bitaxeorg/supraHex/3d/TL3340AF160QG.step

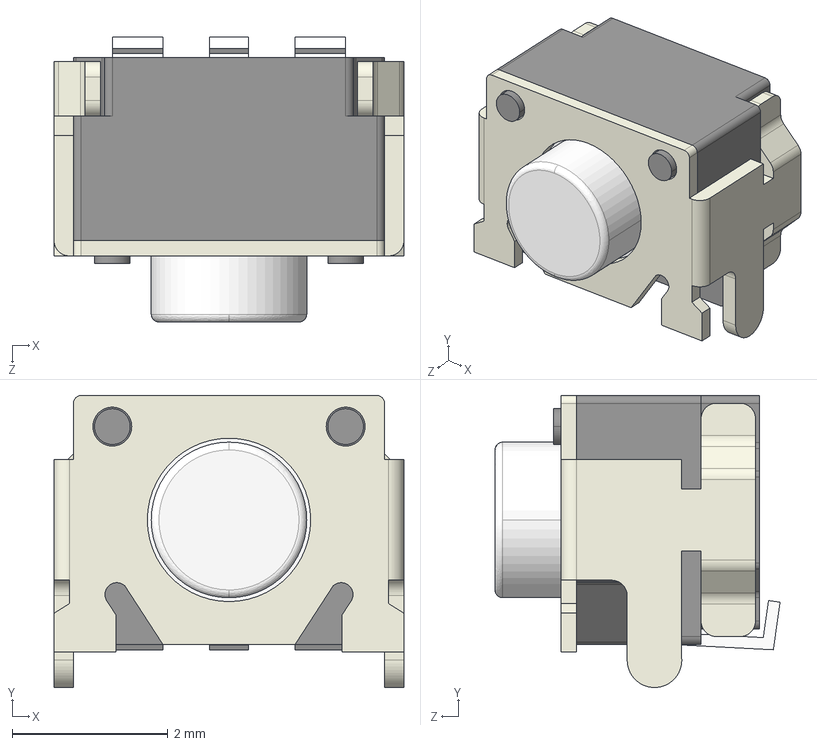
[picture p22: CAD file, 2024-08-30]
3d/TL3340AF160QG.step
4.50 x 3.76 x 3.67 mm
