bitaxeorg/supraHex/3d/heatsink.step

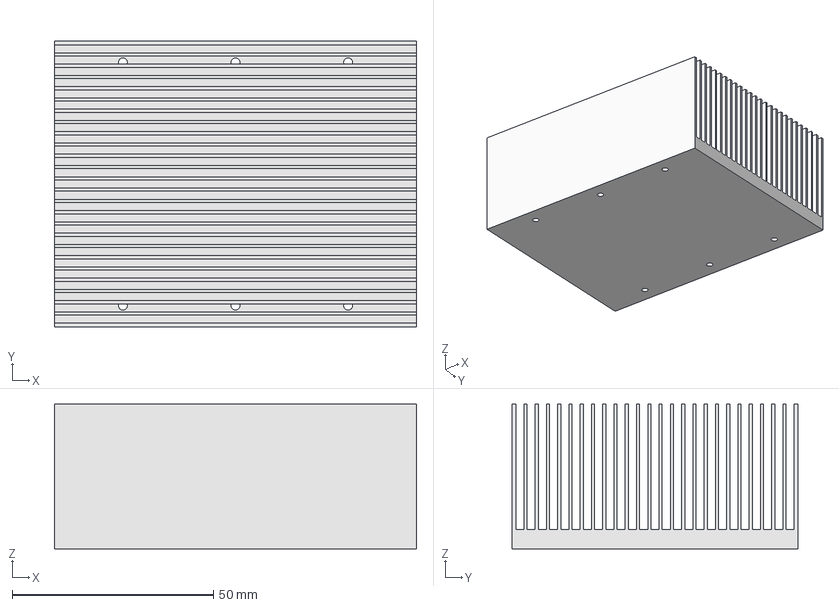
[picture p24: CAD file, 2024-08-30]
3d/heatsink.step
90.0 x 71.0 x 36.0 mm
