bitaxeorg/supraHex/3d/SN74AXC1T45DBVR.STEP

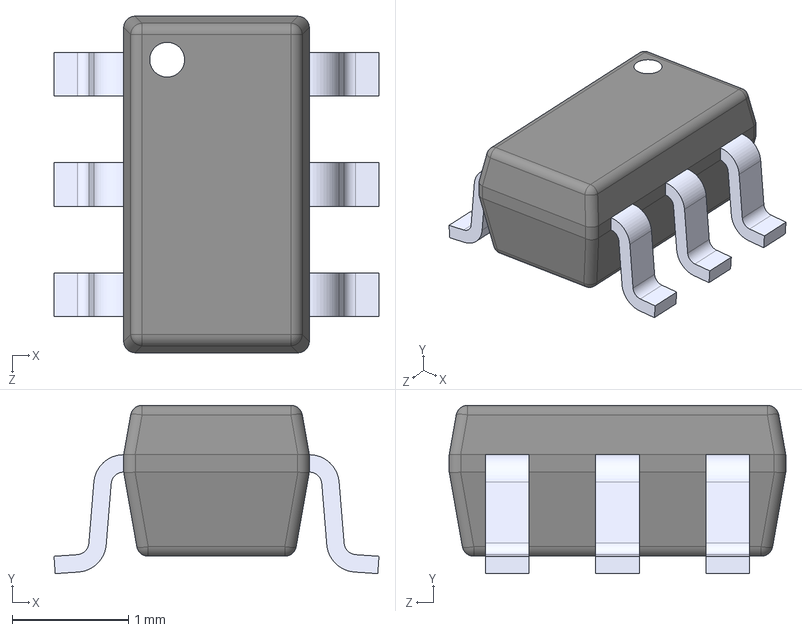
[picture p25: CAD file, 2024-08-30]
3d/SN74AXC1T45DBVR.STEP
2.80 x 1.45 x 2.90 mm
