bitaxeorg/supraHex/3d/RUM0016A.stp

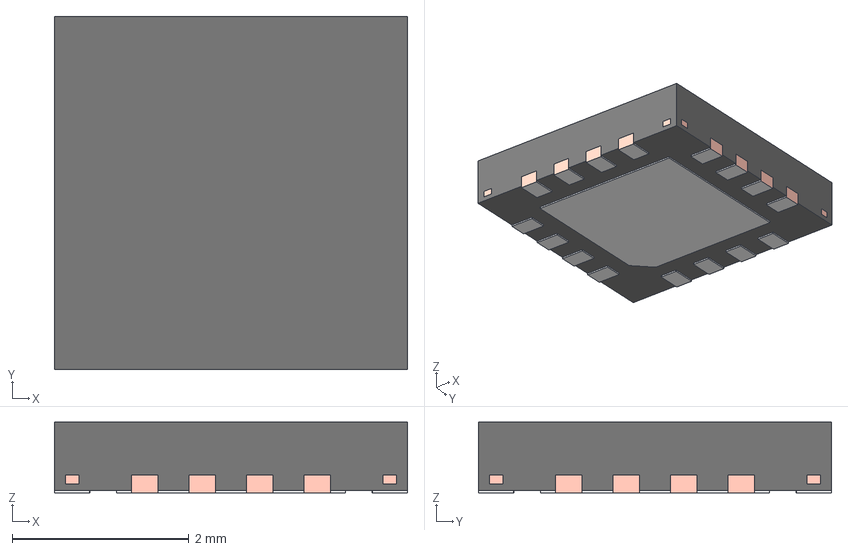
[picture p28: CAD file, 2024-08-30]
3d/RUM0016A.stp
4.00 x 4.00 x 0.8 mm
FRAME
PIN1_AREA
