bitaxeorg/supraHex/3d/bm1366.STP

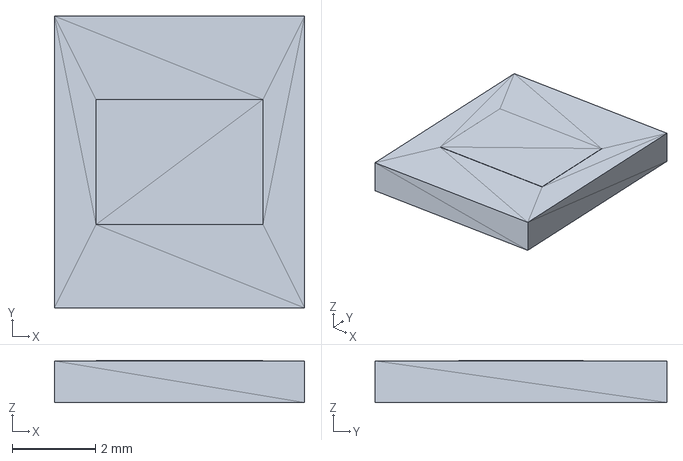
[picture p29: CAD file, 2024-08-30]
3d/bm1366.STP
6.00 x 7.00 x 1.01 mm
