bitaxeorg/supraHex/3d/EVQ-9P701P.stp

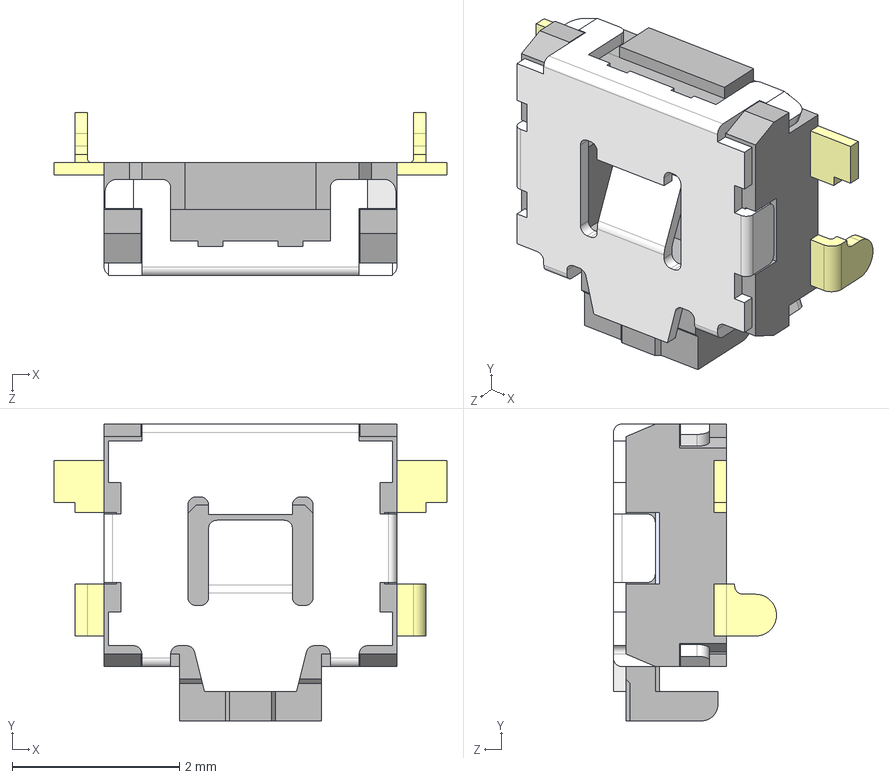
[picture p30: CAD file, 2024-08-30]
3d/EVQ-9P701P.stp
4.70 x 3.55 x 1.95 mm
