bitaxeorg/supraHex/3d/SMV_z90.stp

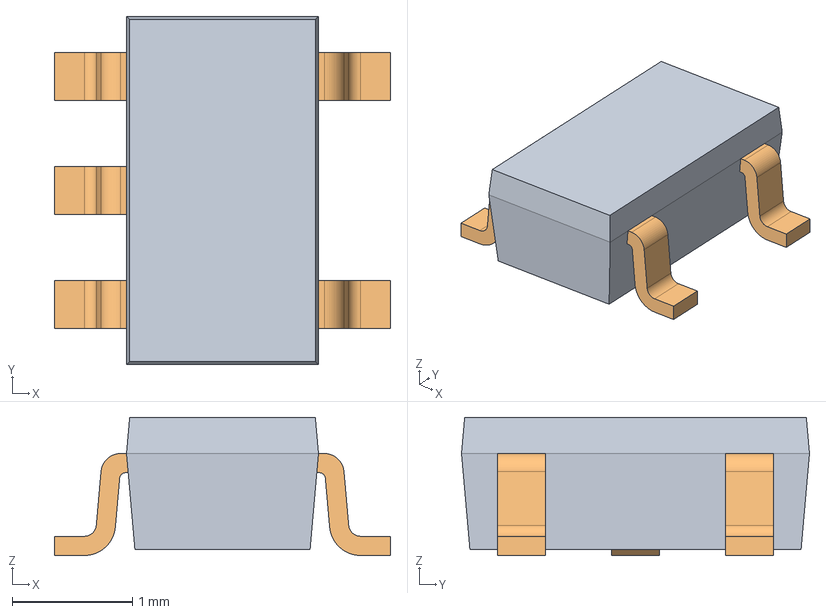
[picture p33: CAD file, 2024-08-30]
3d/SMV_z90.stp
2.80 x 2.90 x 1.15 mm
