bitaxeorg/supraHex/3d/21-0066J_20_MXM.step

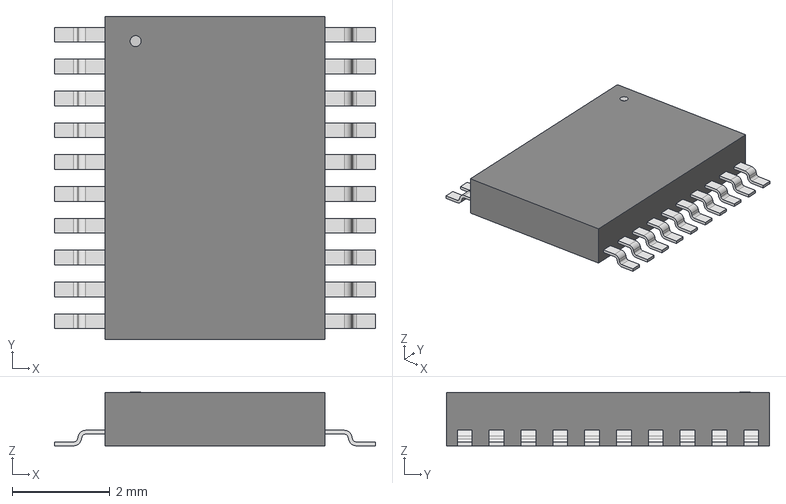
[picture p34: CAD file, 2024-08-30]
3d/21-0066J_20_MXM.step
6.55 x 6.60 x 1.09 mm
