bitaxeorg/supraHex/3d/3225-oscillator.step

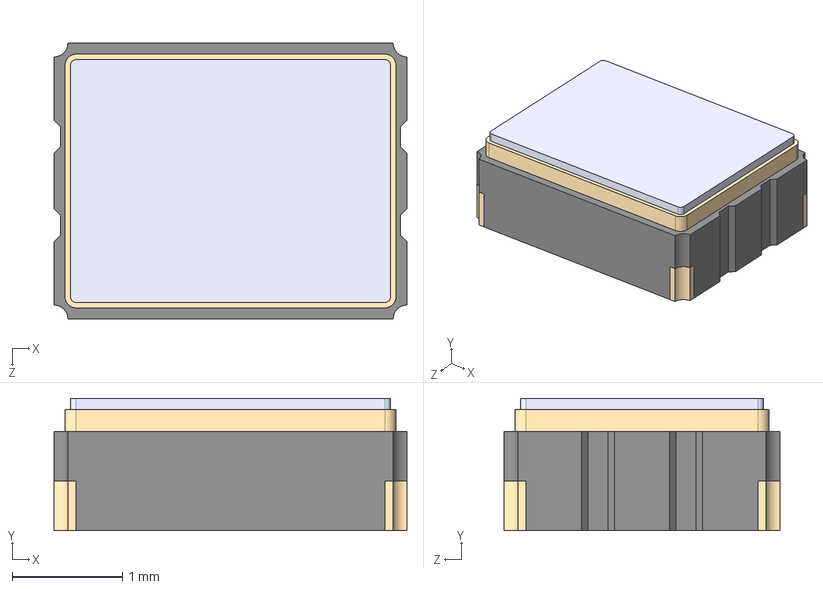
[picture p38: CAD file, 2024-08-30]
3d/3225-oscillator.step
3.20 x 1.20 x 2.50 mm
